telzo2000/cool836pico/img/img00001.jpg

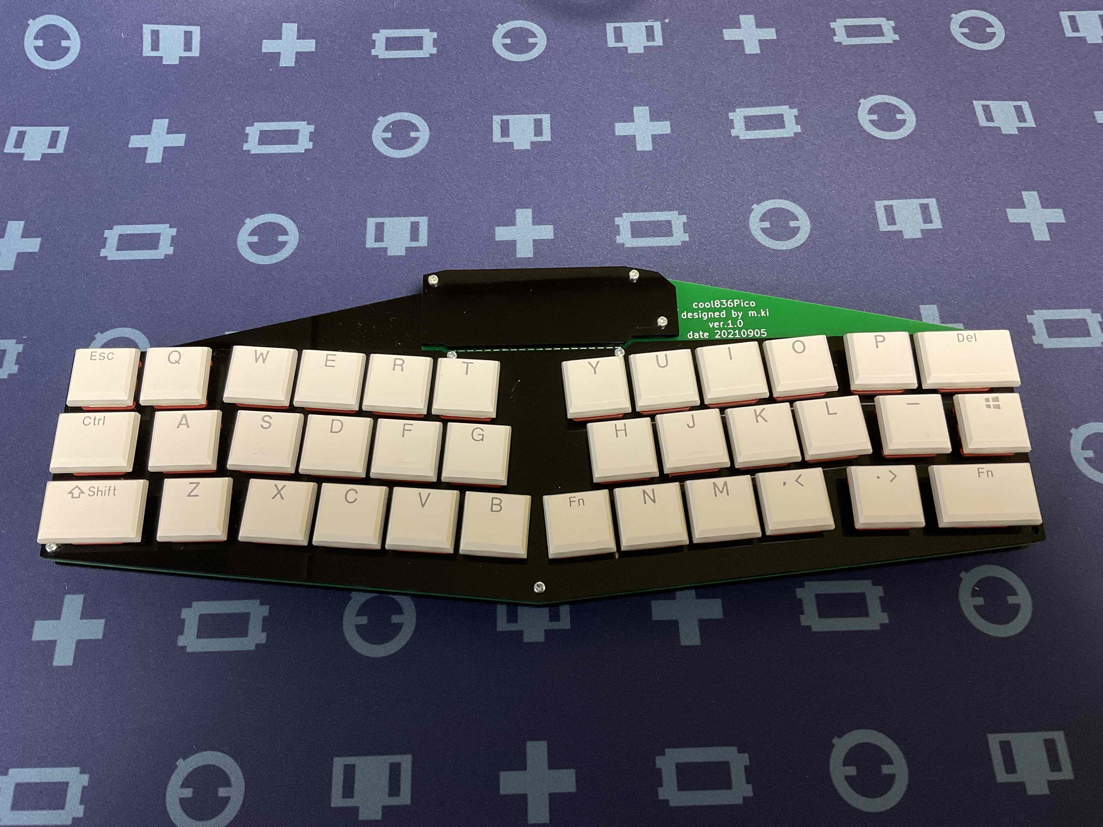
img/img00001.jpg
